serenebliss0/wavelet/src/mini/audio/drivers/Es8311Wire.cpp

#include "Es8311Wire.h"
#include <Wire.h>
#include <Arduino.h>

// -----------------------------------------------------------------------
// Register map (from Espressif's es8311_reg.h -- only what we use here)
// -----------------------------------------------------------------------
namespace
{
    constexpr uint8_t REG_RESET          = 0x00;
    constexpr uint8_t REG_CLK_MANAGER_01 = 0x01;
    constexpr uint8_t REG_CLK_MANAGER_02 = 0x02;
    constexpr uint8_t REG_CLK_MANAGER_03 = 0x03;
    constexpr uint8_t REG_CLK_MANAGER_04 = 0x04;
    constexpr uint8_t REG_CLK_MANAGER_05 = 0x05;
    constexpr uint8_t REG_CLK_MANAGER_06 = 0x06;
    constexpr uint8_t REG_CLK_MANAGER_07 = 0x07;
    constexpr uint8_t REG_CLK_MANAGER_08 = 0x08;
    constexpr uint8_t REG_SDPIN_09       = 0x09;
    constexpr uint8_t REG_SDPOUT_0A      = 0x0A;
    constexpr uint8_t REG_SYSTEM_0D      = 0x0D;
    constexpr uint8_t REG_SYSTEM_0E      = 0x0E;
    constexpr uint8_t REG_SYSTEM_12      = 0x12;
    constexpr uint8_t REG_SYSTEM_13      = 0x13;
    constexpr uint8_t REG_SYSTEM_14      = 0x14;
    constexpr uint8_t REG_ADC_16         = 0x16;
    constexpr uint8_t REG_ADC_17         = 0x17;
    constexpr uint8_t REG_ADC_1C         = 0x1C;
    constexpr uint8_t REG_DAC_31         = 0x31;
    constexpr uint8_t REG_DAC_32         = 0x32;
    constexpr uint8_t REG_DAC_37         = 0x37;

    // Clock coefficient table -- copied verbatim from Espressif's reference
    // driver. Same MCLK/rate combos, same divider values. This is just data,
    // the chip's datasheet dictates these, so it's ported as-is.
    struct CoeffDiv
    {
        uint32_t mclk;
        uint32_t rate;
        uint8_t  pre_div;
        uint8_t  pre_multi;
        uint8_t  adc_div;
        uint8_t  dac_div;
        uint8_t  fs_mode;
        uint8_t  lrck_h;
        uint8_t  lrck_l;
        uint8_t  bclk_div;
        uint8_t  adc_osr;
        uint8_t  dac_osr;
    };

    const CoeffDiv kCoeffDiv[] = {
        // 8k
        {12288000, 8000, 0x06, 0x00, 0x01, 0x01, 0x00, 0x00, 0xff, 0x04, 0x10, 0x10},
        {18432000, 8000, 0x03, 0x01, 0x03, 0x03, 0x00, 0x05, 0xff, 0x18, 0x10, 0x10},
        {16384000, 8000, 0x08, 0x00, 0x01, 0x01, 0x00, 0x00, 0xff, 0x04, 0x10, 0x10},
        {8192000,  8000, 0x04, 0x00, 0x01, 0x01, 0x00, 0x00, 0xff, 0x04, 0x10, 0x10},
        {6144000,  8000, 0x03, 0x00, 0x01, 0x01, 0x00, 0x00, 0xff, 0x04, 0x10, 0x10},
        {4096000,  8000, 0x02, 0x00, 0x01, 0x01, 0x00, 0x00, 0xff, 0x04, 0x10, 0x10},
        {3072000,  8000, 0x01, 0x00, 0x01, 0x01, 0x00, 0x00, 0xff, 0x04, 0x10, 0x10},
        {2048000,  8000, 0x01, 0x00, 0x01, 0x01, 0x00, 0x00, 0xff, 0x04, 0x10, 0x10},
        {1536000,  8000, 0x03, 0x02, 0x01, 0x01, 0x00, 0x00, 0xff, 0x04, 0x10, 0x10},
        {1024000,  8000, 0x01, 0x01, 0x01, 0x01, 0x00, 0x00, 0xff, 0x04, 0x10, 0x10},

        // 11.025k
        {11289600, 11025, 0x04, 0x00, 0x01, 0x01, 0x00, 0x00, 0xff, 0x04, 0x10, 0x10},
        {5644800,  11025, 0x02, 0x00, 0x01, 0x01, 0x00, 0x00, 0xff, 0x04, 0x10, 0x10},
        {2822400,  11025, 0x01, 0x00, 0x01, 0x01, 0x00, 0x00, 0xff, 0x04, 0x10, 0x10},
        {1411200,  11025, 0x01, 0x01, 0x01, 0x01, 0x00, 0x00, 0xff, 0x04, 0x10, 0x10},

        // 12k
        {12288000, 12000, 0x04, 0x00, 0x01, 0x01, 0x00, 0x00, 0xff, 0x04, 0x10, 0x10},
        {6144000,  12000, 0x02, 0x00, 0x01, 0x01, 0x00, 0x00, 0xff, 0x04, 0x10, 0x10},
        {3072000,  12000, 0x01, 0x00, 0x01, 0x01, 0x00, 0x00, 0xff, 0x04, 0x10, 0x10},
        {1536000,  12000, 0x01, 0x01, 0x01, 0x01, 0x00, 0x00, 0xff, 0x04, 0x10, 0x10},

        // 16k
        {12288000, 16000, 0x03, 0x00, 0x01, 0x01, 0x00, 0x00, 0xff, 0x04, 0x10, 0x10},
        {18432000, 16000, 0x03, 0x01, 0x03, 0x03, 0x00, 0x02, 0xff, 0x0c, 0x10, 0x10},
        {16384000, 16000, 0x04, 0x00, 0x01, 0x01, 0x00, 0x00, 0xff, 0x04, 0x10, 0x10},
        {8192000,  16000, 0x02, 0x00, 0x01, 0x01, 0x00, 0x00, 0xff, 0x04, 0x10, 0x10},
        {6144000,  16000, 0x03, 0x01, 0x01, 0x01, 0x00, 0x00, 0xff, 0x04, 0x10, 0x10},
        {4096000,  16000, 0x01, 0x00, 0x01, 0x01, 0x00, 0x00, 0xff, 0x04, 0x10, 0x10},
        {3072000,  16000, 0x03, 0x02, 0x01, 0x01, 0x00, 0x00, 0xff, 0x04, 0x10, 0x10},
        {2048000,  16000, 0x01, 0x01, 0x01, 0x01, 0x00, 0x00, 0xff, 0x04, 0x10, 0x10},
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
        {5644800,  88200, 0x01, 0x02, 0x01, 0x01, 0x00, 0x00, 0xff, 0x04, 0x10, 0x10},
        {2822400,  88200, 0x01, 0x03, 0x01, 0x01, 0x00, 0x00, 0xff, 0x04, 0x10, 0x10},
        {1411200,  88200, 0x01, 0x03, 0x01, 0x01, 0x01, 0x00, 0x7f, 0x02, 0x10, 0x10},

        // 96k
        {12288000, 96000, 0x01, 0x01, 0x01, 0x01, 0x00, 0x00, 0xff, 0x04, 0x10, 0x10},
        {18432000, 96000, 0x03, 0x02, 0x01, 0x01, 0x00, 0x00, 0xff, 0x04, 0x10, 0x10},
        {6144000,  96000, 0x01, 0x02, 0x01, 0x01, 0x00, 0x00, 0xff, 0x04, 0x10, 0x10},
        {3072000,  96000, 0x01, 0x03, 0x01, 0x01, 0x00, 0x00, 0xff, 0x04, 0x10, 0x10},
        {1536000,  96000, 0x01, 0x03, 0x01, 0x01, 0x01, 0x00, 0x7f, 0x02, 0x10, 0x10},
    };

    int getCoeff(uint32_t mclk, uint32_t rate)
    {
        for (size_t i = 0; i < sizeof(kCoeffDiv) / sizeof(kCoeffDiv[0]); i++)
        {
            if (kCoeffDiv[i].rate == rate && kCoeffDiv[i].mclk == mclk)
                return (int)i;
        }
        return -1;
    }

    uint8_t resolutionBits(Es8311Resolution res)
    {
        switch (res)
        {
            case Es8311Resolution::Res16: return 3 << 2;
            case Es8311Resolution::Res18: return 2 << 2;
            case Es8311Resolution::Res20: return 1 << 2;
            case Es8311Resolution::Res24: return 0 << 2;
            case Es8311Resolution::Res32: return 4 << 2;
        }
        return 3 << 2;
    }
}

bool Es8311Codec::writeReg(uint8_t reg, uint8_t val)
{
    Wire.beginTransmission(addr);
    Wire.write(reg);
    Wire.write(val);
    return Wire.endTransmission() == 0;
}

bool Es8311Codec::readReg(uint8_t reg, uint8_t* valOut)
{
    Wire.beginTransmission(addr);
    Wire.write(reg);
    if (Wire.endTransmission(false) != 0) // repeated start, keep bus held
        return false;

    if (Wire.requestFrom((int)addr, 1) != 1)
        return false;

    *valOut = Wire.read();
    return true;
}

bool Es8311Codec::sampleFrequencyConfig(int mclkFrequency, int sampleFrequency)
{
    int coeff = getCoeff((uint32_t)mclkFrequency, (uint32_t)sampleFrequency);
    if (coeff < 0)
        return false; // no matching row -- this MCLK/rate combo isn't supported by the chip

    const CoeffDiv& c = kCoeffDiv[coeff];
    uint8_t regv;

    if (!readReg(REG_CLK_MANAGER_02, &regv)) return false;
    regv &= 0x07;
    regv |= (c.pre_div - 1) << 5;
    regv |= c.pre_multi << 3;
    if (!writeReg(REG_CLK_MANAGER_02, regv)) return false;

    if (!writeReg(REG_CLK_MANAGER_03, (c.fs_mode << 6) | c.adc_osr)) return false;
    if (!writeReg(REG_CLK_MANAGER_04, c.dac_osr)) return false;
    if (!writeReg(REG_CLK_MANAGER_05, ((c.adc_div - 1) << 4) | (c.dac_div - 1))) return false;

    if (!readReg(REG_CLK_MANAGER_06, &regv)) return false;
    regv &= 0xE0;
    regv |= (c.bclk_div < 19) ? (c.bclk_div - 1) : c.bclk_div;
    if (!writeReg(REG_CLK_MANAGER_06, regv)) return false;

    if (!readReg(REG_CLK_MANAGER_07, &regv)) return false;
    regv &= 0xC0;
    regv |= c.lrck_h;
    if (!writeReg(REG_CLK_MANAGER_07, regv)) return false;

    if (!writeReg(REG_CLK_MANAGER_08, c.lrck_l)) return false;

    return true;
}

bool Es8311Codec::clockConfig(const Es8311ClockConfig& clkCfg, Es8311Resolution res)
{
    uint8_t reg06;
    uint8_t reg01 = 0x3F; // enable all internal clocks
    int mclkHz;

    if (clkCfg.mclk_from_mclk_pin)
    {
        mclkHz = clkCfg.mclk_frequency;
    }
    else
    {
        mclkHz = clkCfg.sample_frequency * (int)res * 2;
        reg01 |= (1 << 7); // take clock from BCLK/SCK pin instead
    }

    if (clkCfg.mclk_inverted)
        reg01 |= (1 << 6);

    if (!writeReg(REG_CLK_MANAGER_01, reg01)) return false;

    if (!readReg(REG_CLK_MANAGER_06, &reg06)) return false;
    if (clkCfg.sclk_inverted)
        reg06 |= (1 << 5);
    else
        reg06 &= ~(1 << 5);
    if (!writeReg(REG_CLK_MANAGER_06, reg06)) return false;

    return sampleFrequencyConfig(mclkHz, clkCfg.sample_frequency);
}

bool Es8311Codec::fmtConfig(Es8311Resolution resIn, Es8311Resolution resOut)
{
    uint8_t reg00;
    if (!readReg(REG_RESET, &reg00)) return false;
    reg00 &= 0xBF; // slave serial port mode (default)
    if (!writeReg(REG_RESET, reg00)) return false;

    uint8_t reg09 = resolutionBits(resIn);
    uint8_t reg0a = resolutionBits(resOut);

    if (!writeReg(REG_SDPIN_09, reg09)) return false;
    if (!writeReg(REG_SDPOUT_0A, reg0a)) return false;

    return true;
}

bool Es8311Codec::init(uint8_t i2cAddr, const Es8311ClockConfig& clkCfg,
                        Es8311Resolution resIn, Es8311Resolution resOut)
{
    addr = i2cAddr;

    if (clkCfg.sample_frequency < 8000 || clkCfg.sample_frequency > 96000)
        return false;

    if (!clkCfg.mclk_from_mclk_pin && resIn != resOut)
        return false; // driver requires matching in/out resolution when clocking off SCK

    // Reset to default, then power on.
    if (!writeReg(REG_RESET, 0x1F)) return false;
    delay(20);
    if (!writeReg(REG_RESET, 0x00)) return false;
    if (!writeReg(REG_RESET, 0x80)) return false;

    if (!clockConfig(clkCfg, resOut)) return false;
    if (!fmtConfig(resIn, resOut)) return false;

    if (!writeReg(REG_SYSTEM_0D, 0x01)) return false; // power up analog circuitry
    if (!writeReg(REG_SYSTEM_0E, 0x02)) return false; // enable analog PGA + ADC modulator
    if (!writeReg(REG_SYSTEM_12, 0x00)) return false; // power up DAC
    if (!writeReg(REG_SYSTEM_13, 0x10)) return false; // enable output to speaker/HP drive
    if (!writeReg(REG_ADC_1C, 0x6A)) return false;     // ADC equalizer bypass, cancel DC offset
    if (!writeReg(REG_DAC_37, 0x08)) return false;     // bypass DAC equalizer

    return true;
}

bool Es8311Codec::volumeSet(int volume, int* volumeSetOut)
{
    if (volume < 0) volume = 0;
    if (volume > 100) volume = 100;

    uint8_t reg32 = (volume == 0) ? 0 : (uint8_t)(((volume) * 256 / 100) - 1);

    if (volumeSetOut != nullptr)
        *volumeSetOut = volume;

    return writeReg(REG_DAC_32, reg32);
}

bool Es8311Codec::volumeGet(int* volumeOut)
{
    uint8_t reg32;
    if (!readReg(REG_DAC_32, &reg32)) return false;

    *volumeOut = (reg32 == 0) ? 0 : ((reg32 * 100) / 256) + 1;
    return true;
}

bool Es8311Codec::voiceMute(bool enable)
{
    uint8_t reg31;
    if (!readReg(REG_DAC_31, &reg31)) return false;

    if (enable)
        reg31 |= (1 << 6) | (1 << 5);
    else
        reg31 &= ~((1 << 6) | (1 << 5));

    return writeReg(REG_DAC_31, reg31);
}

bool Es8311Codec::microphoneConfig(bool digitalMic)
{
    uint8_t reg14 = 0x1A; // matches reference driver default
    if (digitalMic)
        reg14 |= (1 << 6);

    if (!writeReg(REG_ADC_17, 0xA8)) return false; // matches reference driver, harmless with mic unused
    return writeReg(REG_SYSTEM_14, reg14);
}
