serenebliss0/wavelet/src/mini/display/touch.cpp

#include "touch.h"

int touch_last_x = 0, touch_last_y = 0;
unsigned short int width=0, height=0, rotation,min_x=0,max_x=0,min_y=0,max_y=0;

FT6336 ts = FT6336(TOUCH_FT6336_SDA, TOUCH_FT6336_SCL, TOUCH_FT6336_INT, TOUCH_FT6336_RST, max(TOUCH_MAP_X1, TOUCH_MAP_X2), max(TOUCH_MAP_Y1, TOUCH_MAP_Y2));

void touch_init(unsigned short int w, unsigned short int h,unsigned char r)
{
  width = w; 
  height = h;
  switch (r){
    case ROTATION_NORMAL:
    case ROTATION_INVERTED:
      min_x = TOUCH_MAP_X1;
      max_x = TOUCH_MAP_X2;
      min_y = TOUCH_MAP_Y1;
      max_y = TOUCH_MAP_Y2;
      break;
    case ROTATION_LEFT:
    case ROTATION_RIGHT:
      min_x = TOUCH_MAP_Y1;
      max_x = TOUCH_MAP_Y2;
      min_y = TOUCH_MAP_X1;
      max_y = TOUCH_MAP_X2;
      break;
    default:
      break;
  }
  ts.begin();
  ts.setRotation(r);
}

bool touch_touched(void)
{
   ts.read();
  if (ts.isTouched)
  {
//#if defined(TOUCH_SWAP_XY)
//    touch_last_x = map(ts.points[0].y, TOUCH_MAP_X1, TOUCH_MAP_X2, 0, width - 1);
//    touch_last_y = map(ts.points[0].x, TOUCH_MAP_Y1, TOUCH_MAP_Y2, 0, height - 1);
//#else
    touch_last_x = map(ts.points[0].x, min_x, max_x, 0, width - 1);
    touch_last_y = map(ts.points[0].y, min_y, max_y, 0, height - 1);
//#endif
//    Serial.print("x = ");
//    Serial.print(touch_last_x);
//    Serial.print(", y = ");
//    Serial.print(touch_last_y);
//    Serial.print("\r\n");
    return true;
  }
  else
  {
    return false;
  }
}

bool touch_has_signal(void)
{
  return true;
}

bool touch_released(void)
{
  return true;
}
