serenebliss0/wavelet/src/mini/storage/Paths.h

namespace Paths
{
    constexpr auto SYSTEM  = "/system";
    constexpr auto CONFIG  = "/config";
    constexpr auto CACHE   = "/cache";
    constexpr auto MEDIA   = "/media";
    constexpr auto LOGS    = "/logs";
    constexpr auto UPDATES = "/updates";

    constexpr auto SETTINGS = "/config/settings.json";
    constexpr auto DEVICE   = "/system/device.json";
    constexpr auto README   = "/README.txt";
}
