serenebliss0/wavelet/src/mini/wavelet-mini-screens/src/ui/ui.c

#include "ui.h"
#include "screens.h"
#include "images.h"
#include "actions.h"
#include "vars.h"

// ASSETS DEFINITION
const uint8_t assets[4652] = {
    0x7E, 0x45, 0x45, 0x5A, 0x03, 0x00, 0x06, 0x00, 0x00, 0x00, 0x00, 0x00, 0x24, 0x00, 0x00, 0x00,
    0x24, 0x00, 0x00, 0x00, 0x00, 0x00, 0x00, 0x00, 0x00, 0x00, 0x00, 0x00, 0x00, 0x00, 0x00, 0x00,
    0x00, 0x00, 0x00, 0x00, 0x20, 0x00, 0x00, 0x00, 0x00, 0x00, 0x00, 0x00, 0x00, 0x00, 0x00, 0x00,
    0x40, 0x01, 0xF0, 0x00, 0x02, 0x00, 0x00, 0x00, 0x24, 0x00, 0x00, 0x00, 0x02, 0x00, 0x00, 0x00,
    0x24, 0x00, 0x00, 0x00, 0x0A, 0x00, 0x00, 0x00, 0x20, 0x00, 0x00, 0x00, 0x0D, 0x00, 0x00, 0x00,
    0xA0, 0x10, 0x00, 0x00, 0x06, 0x00, 0x00, 0x00, 0x38, 0x00, 0x00, 0x00, 0x4C, 0x00, 0x00, 0x00,
    0x54, 0x00, 0x00, 0x00, 0x00, 0x00, 0xFF, 0xFF, 0x58, 0x00, 0x00, 0x00, 0x84, 0x00, 0x00, 0x00,
    0xB0, 0x00, 0x00, 0x00, 0xDC, 0x00, 0x00, 0x00, 0x08, 0x01, 0x00, 0x00, 0x34, 0x01, 0x00, 0x00,
    0x60, 0x01, 0x00, 0x00, 0x8C, 0x01, 0x00, 0x00, 0xB8, 0x01, 0x00, 0x00, 0xE4, 0x01, 0x00, 0x00,
    0x14, 0x02, 0x00, 0x00, 0x20, 0x02, 0x00, 0x00, 0x2C, 0x02, 0x00, 0x00, 0x38, 0x02, 0x00, 0x00,
    0x44, 0x02, 0x00, 0x00, 0x50, 0x02, 0x00, 0x00, 0x5C, 0x02, 0x00, 0x00, 0x0D, 0x00, 0x00, 0x00,
    0x60, 0x02, 0x00, 0x00, 0x78, 0x02, 0x00, 0x00, 0x0D, 0x00, 0x00, 0x00, 0x7C, 0x02, 0x00, 0x00,
    0x02, 0x00, 0x00, 0x00, 0x90, 0x02, 0x00, 0x00, 0x00, 0x00, 0x00, 0x00, 0x00, 0x00, 0x00, 0x00,
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
    { NATIVE_VAR_TYPE_NONE, 0, 0 },
};

ActionExecFunc actions[] = {
    0
};

void ui_init() {
    eez_flow_init(assets, sizeof(assets), (lv_obj_t **)&objects, sizeof(objects), images, sizeof(images), actions);
}

void ui_tick() {
    eez_flow_tick();
    tick_screen(g_currentScreen);
}
