serenebliss0/wavelet/src/mini/wavelet-mini-screens/src/ui/screens.c

#include <string.h>

#include "screens.h"
#include "images.h"
#include "fonts.h"
#include "actions.h"
#include "vars.h"
#include "styles.h"
#include "ui.h"

#include <string.h>

objects_t objects;

static const char *screen_names[] = { "BootSplash", "InitialQRPage", "Onboarding1", "Onboarding2", "Onboarding3", "DefaultClock", "VolumePane" };
static const char *object_names[] = { "boot_splash", "initial_qr_page", "onboarding1", "onboarding2", "onboarding3", "default_clock", "volume_pane", "wavelet_log", "obj0", "obj1", "obj2", "obj3", "obj4", "obj5", "obj6", "obj7", "obj8", "obj9", "obj10", "obj11", "obj12", "obj13", "obj14", "obj15", "obj16", "obj17", "obj18", "obj19", "wallpaper_image", "obj20", "obj21" };

//
// Event handlers
//

lv_obj_t *tick_value_change_obj;

static void event_handler_cb_onboarding1_obj8(lv_event_t *e) {
    lv_event_code_t event = lv_event_get_code(e);
    void *flowState = lv_event_get_user_data(e);
    (void)flowState;
    
    if (event == LV_EVENT_PRESSED) {
        e->user_data = (void *)0;
        flowPropagateValueLVGLEvent(flowState, 4, 0, e);
    }
}

static void event_handler_cb_onboarding2_obj12(lv_event_t *e) {
    lv_event_code_t event = lv_event_get_code(e);
    void *flowState = lv_event_get_user_data(e);
    (void)flowState;
    
    if (event == LV_EVENT_PRESSED) {
        e->user_data = (void *)0;
        flowPropagateValueLVGLEvent(flowState, 4, 0, e);
    }
}

static void event_handler_cb_onboarding3_obj16(lv_event_t *e) {
    lv_event_code_t event = lv_event_get_code(e);
    void *flowState = lv_event_get_user_data(e);
    (void)flowState;
    
    if (event == LV_EVENT_PRESSED) {
        e->user_data = (void *)0;
        flowPropagateValueLVGLEvent(flowState, 4, 0, e);
    }
}

//
// Screens
//

void create_screen_boot_splash() {
    void *flowState = getFlowState(0, 0);
    (void)flowState;
    lv_obj_t *obj = lv_obj_create(0);
    objects.boot_splash = obj;
    lv_obj_set_pos(obj, 0, 0);
    lv_obj_set_size(obj, 320, 240);
    lv_obj_clear_flag(obj, LV_OBJ_FLAG_CLICK_FOCUSABLE|LV_OBJ_FLAG_SNAPPABLE|LV_OBJ_FLAG_SCROLLABLE|LV_OBJ_FLAG_SCROLL_ELASTIC|LV_OBJ_FLAG_SCROLL_CHAIN_HOR);
    lv_obj_set_style_bg_color(obj, lv_color_hex(theme_colors[eez_flow_get_selected_theme_index()][0]), LV_PART_MAIN | LV_STATE_DEFAULT);
    {
        lv_obj_t *parent_obj = obj;
        {
            // wavelet_log
            lv_obj_t *obj = lv_img_create(parent_obj);
            objects.wavelet_log = obj;
            lv_obj_set_pos(obj, 91, 96);
            lv_obj_set_size(obj, LV_SIZE_CONTENT, LV_SIZE_CONTENT);
            lv_img_set_src(obj, &img_wavelet_logo);
            lv_obj_set_style_align(obj, LV_ALIGN_DEFAULT, LV_PART_MAIN | LV_STATE_DEFAULT);
        }
    }
    
    tick_screen_boot_splash();
}

void tick_screen_boot_splash() {
    void *flowState = getFlowState(0, 0);
    (void)flowState;
}

void create_screen_initial_qr_page() {
    void *flowState = getFlowState(0, 1);
    (void)flowState;
    lv_obj_t *obj = lv_obj_create(0);
    objects.initial_qr_page = obj;
    lv_obj_set_pos(obj, 0, 0);
    lv_obj_set_size(obj, 320, 240);
    lv_obj_clear_flag(obj, LV_OBJ_FLAG_CLICK_FOCUSABLE);
    lv_obj_set_style_bg_color(obj, lv_color_hex(theme_colors[eez_flow_get_selected_theme_index()][0]), LV_PART_MAIN | LV_STATE_DEFAULT);
    {
        lv_obj_t *parent_obj = obj;
        {
            lv_obj_t *obj = lv_qrcode_create(parent_obj, 96, lv_color_hex(0x000000), lv_color_hex(0xffffff));
            objects.obj0 = obj;
            lv_obj_set_pos(obj, 10, 72);
            lv_obj_set_size(obj, 96, 96);
            lv_qrcode_update(obj, "{generatedPayloadToken}", 23);
            lv_obj_add_flag(obj, LV_OBJ_FLAG_CLICKABLE);
            lv_obj_set_style_border_color(obj, lv_color_hex(0x000000), LV_PART_MAIN | LV_STATE_DEFAULT);
            lv_obj_set_style_outline_width(obj, 2, LV_PART_MAIN | LV_STATE_DEFAULT);
            lv_obj_set_style_radius(obj, 10, LV_PART_MAIN | LV_STATE_DEFAULT);
            lv_obj_set_style_outline_color(obj, lv_color_hex(theme_colors[eez_flow_get_selected_theme_index()][3]), LV_PART_MAIN | LV_STATE_DEFAULT);
            lv_obj_set_style_outline_opa(obj, 150, LV_PART_MAIN | LV_STATE_DEFAULT);
            lv_obj_set_style_shadow_width(obj, 4, LV_PART_MAIN | LV_STATE_DEFAULT);
            lv_obj_set_style_shadow_color(obj, lv_color_hex(0xff9d9d), LV_PART_MAIN | LV_STATE_DEFAULT);
        }
        {
            lv_obj_t *obj = lv_label_create(parent_obj);
            objects.obj1 = obj;
            lv_obj_set_pos(obj, 127, 72);
            lv_obj_set_size(obj, LV_SIZE_CONTENT, LV_SIZE_CONTENT);
            lv_obj_set_style_text_color(obj, lv_color_hex(theme_colors[eez_flow_get_selected_theme_index()][5]), LV_PART_MAIN | LV_STATE_DEFAULT);
            lv_obj_set_style_text_font(obj, &ui_font_nunito_18_bold, LV_PART_MAIN | LV_STATE_DEFAULT);
            lv_obj_set_style_text_letter_space(obj, 0, LV_PART_MAIN | LV_STATE_DEFAULT);
            lv_label_set_text_static(obj, "Connect to Wavelet");
        }
        {
            lv_obj_t *obj = lv_label_create(parent_obj);
            objects.obj2 = obj;
            lv_obj_set_pos(obj, 127, 98);
            lv_obj_set_size(obj, LV_SIZE_CONTENT, 45);
            lv_obj_set_style_width(obj, 163, LV_PART_MAIN | LV_STATE_DEFAULT);
            lv_obj_set_style_text_color(obj, lv_color_hex(theme_colors[eez_flow_get_selected_theme_index()][5]), LV_PART_MAIN | LV_STATE_DEFAULT);
            lv_obj_set_style_text_font(obj, &ui_font_inter_10, LV_PART_MAIN | LV_STATE_DEFAULT);
            lv_label_set_text_static(obj, "Open the Wavelet app on your phone and scan the QR code, or enter the code below.");
        }
        {
            lv_obj_t *obj = lv_obj_create(parent_obj);
            objects.obj3 = obj;
            lv_obj_set_pos(obj, 127, 143);
            lv_obj_set_size(obj, 163, 57);
            lv_obj_set_style_pad_left(obj, 0, LV_PART_MAIN | LV_STATE_DEFAULT);
            lv_obj_set_style_pad_top(obj, 0, LV_PART_MAIN | LV_STATE_DEFAULT);
            lv_obj_set_style_pad_right(obj, 0, LV_PART_MAIN | LV_STATE_DEFAULT);
            lv_obj_set_style_pad_bottom(obj, 0, LV_PART_MAIN | LV_STATE_DEFAULT);
            lv_obj_set_style_bg_opa(obj, 0, LV_PART_MAIN | LV_STATE_DEFAULT);
            lv_obj_set_style_border_width(obj, 0, LV_PART_MAIN | LV_STATE_DEFAULT);
            lv_obj_set_style_radius(obj, 8, LV_PART_MAIN | LV_STATE_DEFAULT);
            lv_obj_set_style_border_color(obj, lv_color_lighten(lv_color_hex(0x4f762e), 0), LV_PART_MAIN | LV_STATE_DEFAULT);
            lv_obj_set_style_bg_color(obj, lv_color_hex(0xccccff), LV_PART_MAIN | LV_STATE_DEFAULT);
        }
        {
            lv_obj_t *obj = lv_obj_create(parent_obj);
            objects.obj4 = obj;
            lv_obj_set_pos(obj, 127, 143);
            lv_obj_set_size(obj, 163, 57);
            lv_obj_set_style_bg_color(obj, lv_color_hex(0xf04f76), LV_PART_MAIN | LV_STATE_DEFAULT);
            lv_obj_set_style_bg_opa(obj, 20, LV_PART_MAIN | LV_STATE_DEFAULT);
            lv_obj_set_style_border_color(obj, lv_color_hex(0xf04f76), LV_PART_MAIN | LV_STATE_DEFAULT);
            lv_obj_set_style_radius(obj, 8, LV_PART_MAIN | LV_STATE_DEFAULT);
        }
        {
            lv_obj_t *obj = lv_label_create(parent_obj);
            objects.obj5 = obj;
            lv_obj_set_pos(obj, 135, 150);
            lv_obj_set_size(obj, LV_SIZE_CONTENT, LV_SIZE_CONTENT);
            lv_obj_set_style_bg_color(obj, lv_color_hex(theme_colors[eez_flow_get_selected_theme_index()][5]), LV_PART_MAIN | LV_STATE_DEFAULT);
            lv_obj_set_style_text_font(obj, &ui_font_inter_7, LV_PART_MAIN | LV_STATE_DEFAULT);
            lv_obj_set_style_text_color(obj, lv_color_hex(theme_colors[eez_flow_get_selected_theme_index()][5]), LV_PART_MAIN | LV_STATE_DEFAULT);
            lv_obj_set_style_text_letter_space(obj, 2, LV_PART_MAIN | LV_STATE_DEFAULT);
            lv_label_set_text_static(obj, "MANUAL CODE");
        }
        {
            lv_obj_t *obj = lv_label_create(parent_obj);
            objects.obj6 = obj;
            lv_obj_set_pos(obj, 135, 165);
            lv_obj_set_size(obj, LV_SIZE_CONTENT, LV_SIZE_CONTENT);
            lv_obj_set_style_text_color(obj, lv_color_hex(theme_colors[eez_flow_get_selected_theme_index()][5]), LV_PART_MAIN | LV_STATE_DEFAULT);
            lv_obj_set_style_text_font(obj, &lv_font_montserrat_18, LV_PART_MAIN | LV_STATE_DEFAULT);
            lv_label_set_text(obj, "");
        }
    }
    
    tick_screen_initial_qr_page();
}

void tick_screen_initial_qr_page() {
    void *flowState = getFlowState(0, 1);
    (void)flowState;
    {
        const char *new_val = evalTextProperty(flowState, 7, 3, "Failed to evaluate Text in Label widget");
        const char *cur_val = lv_label_get_text(objects.obj6);
        if (strcmp(new_val, cur_val) != 0) {
            tick_value_change_obj = objects.obj6;
            lv_label_set_text(objects.obj6, new_val);
            tick_value_change_obj = NULL;
        }
    }
}

void create_screen_onboarding1() {
    void *flowState = getFlowState(0, 2);
    (void)flowState;
    lv_obj_t *obj = lv_obj_create(0);
    objects.onboarding1 = obj;
    lv_obj_set_pos(obj, 0, 0);
    lv_obj_set_size(obj, 320, 240);
    lv_obj_set_style_bg_color(obj, lv_color_hex(theme_colors[eez_flow_get_selected_theme_index()][0]), LV_PART_MAIN | LV_STATE_DEFAULT);
    {
        lv_obj_t *parent_obj = obj;
        {
            lv_obj_t *obj = lv_label_create(parent_obj);
            objects.obj7 = obj;
            lv_obj_set_pos(obj, 11, 21);
            lv_obj_set_size(obj, LV_SIZE_CONTENT, LV_SIZE_CONTENT);
            lv_obj_set_style_text_font(obj, &ui_font_nunito_18_bold, LV_PART_MAIN | LV_STATE_DEFAULT);
            lv_obj_set_style_text_color(obj, lv_color_hex(theme_colors[eez_flow_get_selected_theme_index()][5]), LV_PART_MAIN | LV_STATE_DEFAULT);
            lv_label_set_text_static(obj, "Quick Settings");
        }
        {
            lv_obj_t *obj = lv_img_create(parent_obj);
            lv_obj_set_pos(obj, 11, 71);
            lv_obj_set_size(obj, LV_SIZE_CONTENT, LV_SIZE_CONTENT);
            lv_img_set_src(obj, &img_onboarding_tutorial_1_swipedown);
        }
        {
            lv_obj_t *obj = lv_img_create(parent_obj);
            lv_obj_set_pos(obj, 114, 217);
            lv_obj_set_size(obj, LV_SIZE_CONTENT, LV_SIZE_CONTENT);
            lv_img_set_src(obj, &img_3_step_guide_phase_1);
        }
        {
            lv_obj_t *obj = lv_btn_create(parent_obj);
            objects.obj8 = obj;
            lv_obj_set_pos(obj, 245, 203);
            lv_obj_set_size(obj, 64, 29);
            lv_obj_add_event_cb(obj, event_handler_cb_onboarding1_obj8, LV_EVENT_ALL, flowState);
            lv_obj_set_style_radius(obj, 7, LV_PART_MAIN | LV_STATE_DEFAULT);
            lv_obj_set_style_bg_color(obj, lv_color_hex(theme_colors[eez_flow_get_selected_theme_index()][2]), LV_PART_MAIN | LV_STATE_DEFAULT);
            {
                lv_obj_t *parent_obj = obj;
                {
                    lv_obj_t *obj = lv_label_create(parent_obj);
                    objects.obj9 = obj;
                    lv_obj_set_pos(obj, 0, 0);
                    lv_obj_set_size(obj, LV_SIZE_CONTENT, LV_SIZE_CONTENT);
                    lv_obj_set_style_align(obj, LV_ALIGN_CENTER, LV_PART_MAIN | LV_STATE_DEFAULT);
                    lv_obj_set_style_text_color(obj, lv_color_hex(theme_colors[eez_flow_get_selected_theme_index()][5]), LV_PART_MAIN | LV_STATE_DEFAULT);
                    lv_obj_set_style_text_font(obj, &lv_font_montserrat_10, LV_PART_MAIN | LV_STATE_DEFAULT);
                    lv_label_set_text_static(obj, "Next");
                }
            }
        }
        {
            lv_obj_t *obj = lv_label_create(parent_obj);
            objects.obj10 = obj;
            lv_obj_set_pos(obj, 134, 80);
            lv_obj_set_size(obj, LV_SIZE_CONTENT, LV_SIZE_CONTENT);
            lv_obj_set_style_text_color(obj, lv_color_hex(theme_colors[eez_flow_get_selected_theme_index()][5]), LV_PART_MAIN | LV_STATE_DEFAULT);
            lv_obj_set_style_text_font(obj, &lv_font_montserrat_12, LV_PART_MAIN | LV_STATE_DEFAULT);
            lv_obj_set_style_width(obj, 172, LV_PART_MAIN | LV_STATE_DEFAULT);
            lv_obj_set_style_text_line_space(obj, 2, LV_PART_MAIN | LV_STATE_DEFAULT);
            lv_label_set_text_static(obj, "Access WiFi, brightness, and Spotify connect with a downward swipe from anywhere on the screen.");
        }
    }
    
    tick_screen_onboarding1();
}

void tick_screen_onboarding1() {
    void *flowState = getFlowState(0, 2);
    (void)flowState;
}

void create_screen_onboarding2() {
    void *flowState = getFlowState(0, 3);
    (void)flowState;
    lv_obj_t *obj = lv_obj_create(0);
    objects.onboarding2 = obj;
    lv_obj_set_pos(obj, 0, 0);
    lv_obj_set_size(obj, 320, 240);
    lv_obj_set_style_bg_color(obj, lv_color_hex(theme_colors[eez_flow_get_selected_theme_index()][0]), LV_PART_MAIN | LV_STATE_DEFAULT);
    {
        lv_obj_t *parent_obj = obj;
        {
            lv_obj_t *obj = lv_label_create(parent_obj);
            objects.obj11 = obj;
            lv_obj_set_pos(obj, 11, 21);
            lv_obj_set_size(obj, LV_SIZE_CONTENT, LV_SIZE_CONTENT);
            lv_obj_set_style_text_font(obj, &ui_font_nunito_18_bold, LV_PART_MAIN | LV_STATE_DEFAULT);
            lv_obj_set_style_text_color(obj, lv_color_hex(theme_colors[eez_flow_get_selected_theme_index()][5]), LV_PART_MAIN | LV_STATE_DEFAULT);
            lv_label_set_text_static(obj, "Widgets");
        }
        {
            lv_obj_t *obj = lv_img_create(parent_obj);
            lv_obj_set_pos(obj, 11, 71);
            lv_obj_set_size(obj, LV_SIZE_CONTENT, LV_SIZE_CONTENT);
            lv_img_set_src(obj, &img_onboarding_tutorial_2_leftright);
        }
        {
            lv_obj_t *obj = lv_img_create(parent_obj);
            lv_obj_set_pos(obj, 114, 217);
            lv_obj_set_size(obj, LV_SIZE_CONTENT, LV_SIZE_CONTENT);
            lv_img_set_src(obj, &img_3_step_guide_phase_2);
        }
        {
            lv_obj_t *obj = lv_btn_create(parent_obj);
            objects.obj12 = obj;
            lv_obj_set_pos(obj, 245, 203);
            lv_obj_set_size(obj, 64, 29);
            lv_obj_add_event_cb(obj, event_handler_cb_onboarding2_obj12, LV_EVENT_ALL, flowState);
            lv_obj_set_style_radius(obj, 7, LV_PART_MAIN | LV_STATE_DEFAULT);
            lv_obj_set_style_bg_color(obj, lv_color_hex(theme_colors[eez_flow_get_selected_theme_index()][2]), LV_PART_MAIN | LV_STATE_DEFAULT);
            {
                lv_obj_t *parent_obj = obj;
                {
                    lv_obj_t *obj = lv_label_create(parent_obj);
                    objects.obj13 = obj;
                    lv_obj_set_pos(obj, 0, 0);
                    lv_obj_set_size(obj, LV_SIZE_CONTENT, LV_SIZE_CONTENT);
                    lv_obj_set_style_align(obj, LV_ALIGN_CENTER, LV_PART_MAIN | LV_STATE_DEFAULT);
                    lv_obj_set_style_text_color(obj, lv_color_hex(theme_colors[eez_flow_get_selected_theme_index()][5]), LV_PART_MAIN | LV_STATE_DEFAULT);
                    lv_obj_set_style_text_font(obj, &lv_font_montserrat_10, LV_PART_MAIN | LV_STATE_DEFAULT);
                    lv_label_set_text_static(obj, "Next");
                }
            }
        }
        {
            lv_obj_t *obj = lv_label_create(parent_obj);
            objects.obj14 = obj;
            lv_obj_set_pos(obj, 134, 80);
            lv_obj_set_size(obj, LV_SIZE_CONTENT, LV_SIZE_CONTENT);
            lv_obj_set_style_text_color(obj, lv_color_hex(theme_colors[eez_flow_get_selected_theme_index()][5]), LV_PART_MAIN | LV_STATE_DEFAULT);
            lv_obj_set_style_text_font(obj, &lv_font_montserrat_12, LV_PART_MAIN | LV_STATE_DEFAULT);
            lv_obj_set_style_width(obj, 172, LV_PART_MAIN | LV_STATE_DEFAULT);
            lv_obj_set_style_text_line_space(obj, 2, LV_PART_MAIN | LV_STATE_DEFAULT);
            lv_label_set_text_static(obj, "Browse your widgets: weather, timers, and more by swiping left or right on the main screen.");
        }
    }
    
    tick_screen_onboarding2();
}

void tick_screen_onboarding2() {
    void *flowState = getFlowState(0, 3);
    (void)flowState;
}

void create_screen_onboarding3() {
    void *flowState = getFlowState(0, 4);
    (void)flowState;
    lv_obj_t *obj = lv_obj_create(0);
    objects.onboarding3 = obj;
    lv_obj_set_pos(obj, 0, 0);
    lv_obj_set_size(obj, 320, 240);
    lv_obj_set_style_bg_color(obj, lv_color_hex(theme_colors[eez_flow_get_selected_theme_index()][0]), LV_PART_MAIN | LV_STATE_DEFAULT);
    {
        lv_obj_t *parent_obj = obj;
        {
            lv_obj_t *obj = lv_label_create(parent_obj);
            objects.obj15 = obj;
            lv_obj_set_pos(obj, 11, 21);
            lv_obj_set_size(obj, LV_SIZE_CONTENT, LV_SIZE_CONTENT);
            lv_obj_set_style_text_font(obj, &ui_font_nunito_18_bold, LV_PART_MAIN | LV_STATE_DEFAULT);
            lv_obj_set_style_text_color(obj, lv_color_hex(theme_colors[eez_flow_get_selected_theme_index()][5]), LV_PART_MAIN | LV_STATE_DEFAULT);
            lv_label_set_text_static(obj, "Always On Clock");
        }
        {
            lv_obj_t *obj = lv_img_create(parent_obj);
            lv_obj_set_pos(obj, 11, 71);
            lv_obj_set_size(obj, LV_SIZE_CONTENT, LV_SIZE_CONTENT);
            lv_img_set_src(obj, &img_onboarding_tutorial_3_swipeup);
        }
        {
            lv_obj_t *obj = lv_img_create(parent_obj);
            lv_obj_set_pos(obj, 114, 217);
            lv_obj_set_size(obj, LV_SIZE_CONTENT, LV_SIZE_CONTENT);
            lv_img_set_src(obj, &img_3_step_guide_phase_3);
        }
        {
            lv_obj_t *obj = lv_btn_create(parent_obj);
            objects.obj16 = obj;
            lv_obj_set_pos(obj, 245, 203);
            lv_obj_set_size(obj, 64, 29);
            lv_obj_add_event_cb(obj, event_handler_cb_onboarding3_obj16, LV_EVENT_ALL, flowState);
            lv_obj_set_style_radius(obj, 7, LV_PART_MAIN | LV_STATE_DEFAULT);
            lv_obj_set_style_bg_color(obj, lv_color_hex(theme_colors[eez_flow_get_selected_theme_index()][1]), LV_PART_MAIN | LV_STATE_DEFAULT);
            {
                lv_obj_t *parent_obj = obj;
                {
                    lv_obj_t *obj = lv_label_create(parent_obj);
                    objects.obj17 = obj;
                    lv_obj_set_pos(obj, 0, 0);
                    lv_obj_set_size(obj, LV_SIZE_CONTENT, LV_SIZE_CONTENT);
                    lv_obj_set_style_align(obj, LV_ALIGN_CENTER, LV_PART_MAIN | LV_STATE_DEFAULT);
                    lv_obj_set_style_text_color(obj, lv_color_hex(theme_colors[eez_flow_get_selected_theme_index()][5]), LV_PART_MAIN | LV_STATE_DEFAULT);
                    lv_obj_set_style_text_font(obj, &lv_font_montserrat_10, LV_PART_MAIN | LV_STATE_DEFAULT);
                    lv_label_set_text_static(obj, "Finish");
                }
            }
        }
        {
            lv_obj_t *obj = lv_label_create(parent_obj);
            objects.obj18 = obj;
            lv_obj_set_pos(obj, 134, 80);
            lv_obj_set_size(obj, LV_SIZE_CONTENT, LV_SIZE_CONTENT);
            lv_obj_set_style_text_color(obj, lv_color_hex(theme_colors[eez_flow_get_selected_theme_index()][5]), LV_PART_MAIN | LV_STATE_DEFAULT);
            lv_obj_set_style_text_font(obj, &lv_font_montserrat_12, LV_PART_MAIN | LV_STATE_DEFAULT);
            lv_obj_set_style_width(obj, 172, LV_PART_MAIN | LV_STATE_DEFAULT);
            lv_obj_set_style_text_line_space(obj, 2, LV_PART_MAIN | LV_STATE_DEFAULT);
            lv_label_set_text_static(obj, "Swipe up for a minimal always-on display that stays visible even when the screen is dimmed.");
        }
    }
    
    tick_screen_onboarding3();
}

void tick_screen_onboarding3() {
    void *flowState = getFlowState(0, 4);
    (void)flowState;
}

void create_screen_default_clock() {
    void *flowState = getFlowState(0, 5);
    (void)flowState;
    lv_obj_t *obj = lv_obj_create(0);
    objects.default_clock = obj;
    lv_obj_set_pos(obj, 0, 0);
    lv_obj_set_size(obj, 320, 240);
    lv_obj_set_style_bg_color(obj, lv_color_hex(theme_colors[eez_flow_get_selected_theme_index()][0]), LV_PART_MAIN | LV_STATE_DEFAULT);
    {
        lv_obj_t *parent_obj = obj;
        {
            lv_obj_t *obj = lv_label_create(parent_obj);
            objects.obj20 = obj;
            lv_obj_set_pos(obj, 21, 13);
            lv_obj_set_size(obj, LV_SIZE_CONTENT, LV_SIZE_CONTENT);
            lv_obj_set_style_width(obj, 1073741823, LV_PART_MAIN | LV_STATE_DEFAULT);
            lv_obj_set_style_height(obj, 1073741823, LV_PART_MAIN | LV_STATE_DEFAULT);
            lv_label_set_text(obj, "");
        }
        {
            lv_obj_t *obj = lv_label_create(parent_obj);
            lv_obj_set_pos(obj, 21, 20);
            lv_obj_set_size(obj, LV_SIZE_CONTENT, LV_SIZE_CONTENT);
            lv_obj_set_style_text_font(obj, &lv_font_montserrat_12, LV_PART_MAIN | LV_STATE_DEFAULT);
            lv_obj_set_style_width(obj, 10193, LV_PART_MAIN | LV_STATE_DEFAULT);
            lv_obj_set_style_height(obj, 10193, LV_PART_MAIN | LV_STATE_DEFAULT);
            lv_label_set_text_static(obj, "");
        }
        {
            lv_obj_t *obj = lv_label_create(parent_obj);
            objects.obj21 = obj;
            lv_obj_set_pos(obj, 38, 20);
            lv_obj_set_size(obj, LV_SIZE_CONTENT, LV_SIZE_CONTENT);
            lv_obj_set_style_text_font(obj, &lv_font_montserrat_12, LV_PART_MAIN | LV_STATE_DEFAULT);
            lv_label_set_text(obj, "");
        }
        {
            lv_obj_t *obj = lv_label_create(parent_obj);
            lv_obj_set_pos(obj, 251, 19);
            lv_obj_set_size(obj, LV_SIZE_CONTENT, LV_SIZE_CONTENT);
            lv_obj_set_style_text_font(obj, &lv_font_montserrat_12, LV_PART_MAIN | LV_STATE_DEFAULT);
            lv_label_set_text_static(obj, "");
        }
        {
            lv_obj_t *obj = lv_label_create(parent_obj);
            lv_obj_set_pos(obj, 282, 20);
            lv_obj_set_size(obj, LV_SIZE_CONTENT, LV_SIZE_CONTENT);
            lv_obj_set_style_text_font(obj, &lv_font_montserrat_12, LV_PART_MAIN | LV_STATE_DEFAULT);
            lv_label_set_text_static(obj, "");
        }
        {
            lv_obj_t *obj = lv_label_create(parent_obj);
            lv_obj_set_pos(obj, 57, 94);
            lv_obj_set_size(obj, LV_SIZE_CONTENT, LV_SIZE_CONTENT);
            lv_obj_set_style_text_font(obj, &lv_font_montserrat_48, LV_PART_MAIN | LV_STATE_DEFAULT);
            lv_label_set_text_static(obj, "hh");
        }
        {
            lv_obj_t *obj = lv_label_create(parent_obj);
            lv_obj_set_pos(obj, 185, 95);
            lv_obj_set_size(obj, LV_SIZE_CONTENT, LV_SIZE_CONTENT);
            lv_obj_set_style_text_font(obj, &lv_font_montserrat_48, LV_PART_MAIN | LV_STATE_DEFAULT);
            lv_label_set_text_static(obj, "hh");
        }
        {
            lv_obj_t *obj = lv_label_create(parent_obj);
            lv_obj_set_pos(obj, 149, 95);
            lv_obj_set_size(obj, LV_SIZE_CONTENT, LV_SIZE_CONTENT);
            lv_obj_set_style_text_font(obj, &lv_font_montserrat_48, LV_PART_MAIN | LV_STATE_DEFAULT);
            lv_label_set_text_static(obj, ":");
        }
        {
            lv_obj_t *obj = lv_label_create(parent_obj);
            lv_obj_set_pos(obj, 147, 161);
            lv_obj_set_size(obj, LV_SIZE_CONTENT, LV_SIZE_CONTENT);
            lv_obj_set_style_text_font(obj, &lv_font_montserrat_14, LV_PART_MAIN | LV_STATE_DEFAULT);
            lv_label_set_text_static(obj, "day");
        }
        {
            lv_obj_t *obj = lv_label_create(parent_obj);
            lv_obj_set_pos(obj, 144, 177);
            lv_obj_set_size(obj, LV_SIZE_CONTENT, LV_SIZE_CONTENT);
            lv_obj_set_style_text_font(obj, &lv_font_montserrat_14, LV_PART_MAIN | LV_STATE_DEFAULT);
            lv_obj_set_style_align(obj, LV_ALIGN_DEFAULT, LV_PART_MAIN | LV_STATE_DEFAULT);
            lv_label_set_text_static(obj, "date");
        }
        {
            lv_obj_t *obj = lv_obj_create(parent_obj);
            objects.obj19 = obj;
            lv_obj_set_pos(obj, 82, 206);
            lv_obj_set_size(obj, 156, 24);
            lv_obj_set_style_bg_color(obj, lv_color_hex(theme_colors[eez_flow_get_selected_theme_index()][2]), LV_PART_MAIN | LV_STATE_DEFAULT);
            lv_obj_set_style_border_color(obj, lv_color_hex(theme_colors[eez_flow_get_selected_theme_index()][3]), LV_PART_MAIN | LV_STATE_DEFAULT);
        }
        {
            lv_obj_t *obj = lv_label_create(parent_obj);
            lv_obj_set_pos(obj, 99, 211);
            lv_obj_set_size(obj, LV_SIZE_CONTENT, LV_SIZE_CONTENT);
            lv_label_set_long_mode(obj, LV_LABEL_LONG_SCROLL);
            lv_obj_set_style_align(obj, LV_ALIGN_DEFAULT, LV_PART_MAIN | LV_STATE_DEFAULT);
            lv_obj_set_style_text_font(obj, &lv_font_montserrat_12, LV_PART_MAIN | LV_STATE_DEFAULT);
            lv_label_set_text_static(obj, "This love is so super");
        }
        {
            // wallpaperImage
            lv_obj_t *obj = lv_obj_create(parent_obj);
            objects.wallpaper_image = obj;
            lv_obj_set_pos(obj, -1, 0);
            lv_obj_set_size(obj, 320, 240);
            lv_obj_set_style_pad_left(obj, 0, LV_PART_MAIN | LV_STATE_DEFAULT);
            lv_obj_set_style_pad_top(obj, 0, LV_PART_MAIN | LV_STATE_DEFAULT);
            lv_obj_set_style_pad_right(obj, 0, LV_PART_MAIN | LV_STATE_DEFAULT);
            lv_obj_set_style_pad_bottom(obj, 0, LV_PART_MAIN | LV_STATE_DEFAULT);
            lv_obj_set_style_bg_opa(obj, 0, LV_PART_MAIN | LV_STATE_DEFAULT);
            lv_obj_set_style_border_width(obj, 0, LV_PART_MAIN | LV_STATE_DEFAULT);
            lv_obj_set_style_radius(obj, 0, LV_PART_MAIN | LV_STATE_DEFAULT);
        }
    }
    
    tick_screen_default_clock();
}

void tick_screen_default_clock() {
    void *flowState = getFlowState(0, 5);
    (void)flowState;
    {
        const char *new_val = evalTextProperty(flowState, 0, 3, "Failed to evaluate Text in Label widget");
        const char *cur_val = lv_label_get_text(objects.obj20);
        if (strcmp(new_val, cur_val) != 0) {
            tick_value_change_obj = objects.obj20;
            lv_label_set_text(objects.obj20, new_val);
            tick_value_change_obj = NULL;
        }
    }
    {
        const char *new_val = evalTextProperty(flowState, 3, 3, "Failed to evaluate Text in Label widget");
        const char *cur_val = lv_label_get_text(objects.obj21);
        if (strcmp(new_val, cur_val) != 0) {
            tick_value_change_obj = objects.obj21;
            lv_label_set_text(objects.obj21, new_val);
            tick_value_change_obj = NULL;
        }
    }
}

void create_screen_volume_pane() {
    void *flowState = getFlowState(0, 6);
    (void)flowState;
    lv_obj_t *obj = lv_obj_create(0);
    objects.volume_pane = obj;
    lv_obj_set_pos(obj, 0, 0);
    lv_obj_set_size(obj, 320, 240);
    lv_obj_set_style_bg_color(obj, lv_color_hex(theme_colors[eez_flow_get_selected_theme_index()][0]), LV_PART_MAIN | LV_STATE_DEFAULT);
    
    tick_screen_volume_pane();
}

void tick_screen_volume_pane() {
    void *flowState = getFlowState(0, 6);
    (void)flowState;
}

typedef void (*tick_screen_func_t)();
tick_screen_func_t tick_screen_funcs[] = {
    tick_screen_boot_splash,
    tick_screen_initial_qr_page,
    tick_screen_onboarding1,
    tick_screen_onboarding2,
    tick_screen_onboarding3,
    tick_screen_default_clock,
    tick_screen_volume_pane,
};
void tick_screen(int screen_index) {
    if (screen_index >= 0 && screen_index < 7) {
        tick_screen_funcs[screen_index]();
    }
}
void tick_screen_by_id(enum ScreensEnum screenId) {
    tick_screen(screenId - 1);
}

//
// Fonts
//

ext_font_desc_t fonts[] = {
    { "Nunito-18", &ui_font_nunito_18 },
    { "Nunito-18 Bold", &ui_font_nunito_18_bold },
    { "Inter-10", &ui_font_inter_10 },
    { "Inter-7", &ui_font_inter_7 },
    { "font_icons", &ui_font_font_icons },
#if LV_FONT_MONTSERRAT_8
    { "MONTSERRAT_8", &lv_font_montserrat_8 },
#endif
#if LV_FONT_MONTSERRAT_10
    { "MONTSERRAT_10", &lv_font_montserrat_10 },
#endif
#if LV_FONT_MONTSERRAT_12
    { "MONTSERRAT_12", &lv_font_montserrat_12 },
#endif
#if LV_FONT_MONTSERRAT_14
    { "MONTSERRAT_14", &lv_font_montserrat_14 },
#endif
#if LV_FONT_MONTSERRAT_16
    { "MONTSERRAT_16", &lv_font_montserrat_16 },
#endif
#if LV_FONT_MONTSERRAT_18
    { "MONTSERRAT_18", &lv_font_montserrat_18 },
#endif
#if LV_FONT_MONTSERRAT_20
    { "MONTSERRAT_20", &lv_font_montserrat_20 },
#endif
#if LV_FONT_MONTSERRAT_22
    { "MONTSERRAT_22", &lv_font_montserrat_22 },
#endif
#if LV_FONT_MONTSERRAT_24
    { "MONTSERRAT_24", &lv_font_montserrat_24 },
#endif
#if LV_FONT_MONTSERRAT_26
    { "MONTSERRAT_26", &lv_font_montserrat_26 },
#endif
#if LV_FONT_MONTSERRAT_28
    { "MONTSERRAT_28", &lv_font_montserrat_28 },
#endif
#if LV_FONT_MONTSERRAT_30
    { "MONTSERRAT_30", &lv_font_montserrat_30 },
#endif
#if LV_FONT_MONTSERRAT_32
    { "MONTSERRAT_32", &lv_font_montserrat_32 },
#endif
#if LV_FONT_MONTSERRAT_34
    { "MONTSERRAT_34", &lv_font_montserrat_34 },
#endif
#if LV_FONT_MONTSERRAT_36
    { "MONTSERRAT_36", &lv_font_montserrat_36 },
#endif
#if LV_FONT_MONTSERRAT_38
    { "MONTSERRAT_38", &lv_font_montserrat_38 },
#endif
#if LV_FONT_MONTSERRAT_40
    { "MONTSERRAT_40", &lv_font_montserrat_40 },
#endif
#if LV_FONT_MONTSERRAT_42
    { "MONTSERRAT_42", &lv_font_montserrat_42 },
#endif
#if LV_FONT_MONTSERRAT_44
    { "MONTSERRAT_44", &lv_font_montserrat_44 },
#endif
#if LV_FONT_MONTSERRAT_46
    { "MONTSERRAT_46", &lv_font_montserrat_46 },
#endif
#if LV_FONT_MONTSERRAT_48
    { "MONTSERRAT_48", &lv_font_montserrat_48 },
#endif
};

//
// Color themes
//

void change_color_theme(uint32_t theme_index) {
    {
        lv_obj_set_style_bg_color(objects.boot_splash, lv_color_hex(theme_colors[theme_index][0]), LV_PART_MAIN | LV_STATE_DEFAULT);
    }
    {
        lv_obj_set_style_bg_color(objects.initial_qr_page, lv_color_hex(theme_colors[theme_index][0]), LV_PART_MAIN | LV_STATE_DEFAULT);
        lv_obj_set_style_outline_color(objects.obj0, lv_color_hex(theme_colors[theme_index][3]), LV_PART_MAIN | LV_STATE_DEFAULT);
        lv_obj_set_style_text_color(objects.obj1, lv_color_hex(theme_colors[theme_index][5]), LV_PART_MAIN | LV_STATE_DEFAULT);
        lv_obj_set_style_text_color(objects.obj2, lv_color_hex(theme_colors[theme_index][5]), LV_PART_MAIN | LV_STATE_DEFAULT);
        lv_obj_set_style_bg_color(objects.obj5, lv_color_hex(theme_colors[theme_index][5]), LV_PART_MAIN | LV_STATE_DEFAULT);
        lv_obj_set_style_text_color(objects.obj5, lv_color_hex(theme_colors[theme_index][5]), LV_PART_MAIN | LV_STATE_DEFAULT);
        lv_obj_set_style_text_color(objects.obj6, lv_color_hex(theme_colors[theme_index][5]), LV_PART_MAIN | LV_STATE_DEFAULT);
    }
    {
        lv_obj_set_style_bg_color(objects.onboarding1, lv_color_hex(theme_colors[theme_index][0]), LV_PART_MAIN | LV_STATE_DEFAULT);
        lv_obj_set_style_text_color(objects.obj7, lv_color_hex(theme_colors[theme_index][5]), LV_PART_MAIN | LV_STATE_DEFAULT);
        lv_obj_set_style_bg_color(objects.obj8, lv_color_hex(theme_colors[theme_index][2]), LV_PART_MAIN | LV_STATE_DEFAULT);
        lv_obj_set_style_text_color(objects.obj9, lv_color_hex(theme_colors[theme_index][5]), LV_PART_MAIN | LV_STATE_DEFAULT);
        lv_obj_set_style_text_color(objects.obj10, lv_color_hex(theme_colors[theme_index][5]), LV_PART_MAIN | LV_STATE_DEFAULT);
    }
    {
        lv_obj_set_style_bg_color(objects.onboarding2, lv_color_hex(theme_colors[theme_index][0]), LV_PART_MAIN | LV_STATE_DEFAULT);
        lv_obj_set_style_text_color(objects.obj11, lv_color_hex(theme_colors[theme_index][5]), LV_PART_MAIN | LV_STATE_DEFAULT);
        lv_obj_set_style_bg_color(objects.obj12, lv_color_hex(theme_colors[theme_index][2]), LV_PART_MAIN | LV_STATE_DEFAULT);
        lv_obj_set_style_text_color(objects.obj13, lv_color_hex(theme_colors[theme_index][5]), LV_PART_MAIN | LV_STATE_DEFAULT);
        lv_obj_set_style_text_color(objects.obj14, lv_color_hex(theme_colors[theme_index][5]), LV_PART_MAIN | LV_STATE_DEFAULT);
    }
    {
        lv_obj_set_style_bg_color(objects.onboarding3, lv_color_hex(theme_colors[theme_index][0]), LV_PART_MAIN | LV_STATE_DEFAULT);
        lv_obj_set_style_text_color(objects.obj15, lv_color_hex(theme_colors[theme_index][5]), LV_PART_MAIN | LV_STATE_DEFAULT);
        lv_obj_set_style_bg_color(objects.obj16, lv_color_hex(theme_colors[theme_index][1]), LV_PART_MAIN | LV_STATE_DEFAULT);
        lv_obj_set_style_text_color(objects.obj17, lv_color_hex(theme_colors[theme_index][5]), LV_PART_MAIN | LV_STATE_DEFAULT);
        lv_obj_set_style_text_color(objects.obj18, lv_color_hex(theme_colors[theme_index][5]), LV_PART_MAIN | LV_STATE_DEFAULT);
    }
    {
        lv_obj_set_style_bg_color(objects.default_clock, lv_color_hex(theme_colors[theme_index][0]), LV_PART_MAIN | LV_STATE_DEFAULT);
        lv_obj_set_style_bg_color(objects.obj19, lv_color_hex(theme_colors[theme_index][2]), LV_PART_MAIN | LV_STATE_DEFAULT);
        lv_obj_set_style_border_color(objects.obj19, lv_color_hex(theme_colors[theme_index][3]), LV_PART_MAIN | LV_STATE_DEFAULT);
    }
    {
        lv_obj_set_style_bg_color(objects.volume_pane, lv_color_hex(theme_colors[theme_index][0]), LV_PART_MAIN | LV_STATE_DEFAULT);
    }
    lv_obj_invalidate(objects.boot_splash);
    lv_obj_invalidate(objects.initial_qr_page);
    lv_obj_invalidate(objects.onboarding1);
    lv_obj_invalidate(objects.onboarding2);
    lv_obj_invalidate(objects.onboarding3);
    lv_obj_invalidate(objects.default_clock);
    lv_obj_invalidate(objects.volume_pane);
}
static const char *theme_names[] = { "Dark Mode", "Light Mode" };
uint32_t theme_colors[2][13] = {
    { 0xff0d0d0d, 0xff1a1a1a, 0xff222222, 0xff2a2a2a, 0xff333333, 0xfff0f0f0, 0xff888888, 0xff444444, 0xff1db954, 0xff4ade80, 0xffffb347, 0xffe63946, 0xffffffff },
    { 0xfffaf1f9, 0xffffffff, 0xffffdef2, 0xfffdb6e1, 0xffe8c8e0, 0xff010a1a, 0xff6b3a6b, 0xffc4a8c4, 0xff1db954, 0xff16a34a, 0xffd97706, 0xffdc2626, 0xffffffff },
};

//
//
//

void create_screens() {
    
    eez_flow_init_fonts(fonts, sizeof(fonts) / sizeof(ext_font_desc_t));
    
    eez_flow_init_themes(theme_names, sizeof(theme_names) / sizeof(const char *), change_color_theme, &theme_colors[0][0], sizeof(theme_colors[0]) / sizeof(uint32_t));

// Set default LVGL theme
    lv_disp_t *dispp = lv_disp_get_default();
    lv_theme_t *theme = lv_theme_default_init(dispp, lv_palette_main(LV_PALETTE_BLUE), lv_palette_main(LV_PALETTE_RED), false, LV_FONT_DEFAULT);
    lv_disp_set_theme(dispp, theme);
    
    // Initialize screens
    eez_flow_init_screen_names(screen_names, sizeof(screen_names) / sizeof(const char *));
    eez_flow_init_object_names(object_names, sizeof(object_names) / sizeof(const char *));
    
    // Create screens
    create_screen_boot_splash();
    create_screen_initial_qr_page();
    create_screen_onboarding1();
    create_screen_onboarding2();
    create_screen_onboarding3();
    create_screen_default_clock();
    create_screen_volume_pane();
}
