serenebliss0/wavelet/src/mini/wavelet-mini-screens/src/ui/ui_font_inter_7.c

/*******************************************************************************
 * Size: 7 px
 * Bpp: 8
 * Opts: --bpp 8 --size 7 --no-compress --font ..\..\..\..\..\..\Inter,Nunito\Inter\Inter-VariableFont_opsz,wght.ttf --range 32-127 --format lvgl
 ******************************************************************************/

#ifdef __has_include
    #if __has_include("lvgl.h")
        #ifndef LV_LVGL_H_INCLUDE_SIMPLE
            #define LV_LVGL_H_INCLUDE_SIMPLE
        #endif
    #endif
#endif

#ifdef LV_LVGL_H_INCLUDE_SIMPLE
    #include "lvgl.h"
#else
    #include "lvgl.h"
#endif

#ifndef UI_FONT_INTER_7
#define UI_FONT_INTER_7 1
#endif

#if UI_FONT_INTER_7

/*-----------------
 *    BITMAPS
 *----------------*/

/*Store the image of the glyphs*/
static LV_ATTRIBUTE_LARGE_CONST const uint8_t glyph_bitmap[] = {
    /* U+0020 " " */

    /* U+0021 "!" */
    0x57, 0x59, 0x53, 0x56, 0x50, 0x53, 0x2b, 0x2d,
    0x4e, 0x50,

    /* U+0022 "\"" */
    0x44, 0x77, 0x86, 0x39, 0x65, 0x7c,

    /* U+0023 "#" */
    0x0, 0x84, 0x0, 0x84, 0x0, 0x4b, 0xff, 0x8f,
    0xff, 0x26, 0x0, 0x83, 0x26, 0x5d, 0x0, 0x8e,
    0xf0, 0xd9, 0xb7, 0x0, 0x46, 0x3d, 0x79, 0xa,
    0x0,

    /* U+0024 "$" */
    0x0, 0x0, 0x49, 0x0, 0x0, 0x1f, 0xa4, 0xff,
    0x7c, 0x0, 0x62, 0x4c, 0x68, 0x32, 0x0, 0x7,
    0x71, 0xf4, 0x53, 0x0, 0x35, 0xe, 0x68, 0xa1,
    0x7, 0x2f, 0xa7, 0xff, 0x8a, 0x0, 0x0, 0x0,
    0x45, 0x0, 0x0,

    /* U+0025 "%" */
    0x1e, 0x97, 0x80, 0x0, 0x6f, 0x25, 0x0, 0xf,
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
    0x52, 0x6f, 0x0, 0x0, 0x96, 0x0, 0x0, 0x9d,
    0x0, 0x0, 0x92, 0xac, 0x0, 0x9c, 0x0, 0x0,
    0x9a, 0x0, 0x52, 0x4e, 0x0,

    /* U+007E "~" */
    0x1c, 0x9c, 0x3a, 0x5a, 0x2, 0x3d, 0x1c, 0x72,
    0x82, 0x0
};

/*---------------------
 *  GLYPH DESCRIPTION
 *--------------------*/

static const lv_font_fmt_txt_glyph_dsc_t glyph_dsc[] = {
    {.bitmap_index = 0, .adv_w = 0, .box_w = 0, .box_h = 0, .ofs_x = 0, .ofs_y = 0} /* id = 0 reserved */,
    {.bitmap_index = 0, .adv_w = 32, .box_w = 0, .box_h = 0, .ofs_x = 0, .ofs_y = 0},
    {.bitmap_index = 0, .adv_w = 32, .box_w = 2, .box_h = 5, .ofs_x = 0, .ofs_y = 0},
    {.bitmap_index = 10, .adv_w = 52, .box_w = 3, .box_h = 2, .ofs_x = 0, .ofs_y = 3},
    {.bitmap_index = 16, .adv_w = 71, .box_w = 5, .box_h = 5, .ofs_x = 0, .ofs_y = 0},
    {.bitmap_index = 41, .adv_w = 72, .box_w = 5, .box_h = 7, .ofs_x = 0, .ofs_y = -1},
    {.bitmap_index = 76, .adv_w = 110, .box_w = 7, .box_h = 5, .ofs_x = 0, .ofs_y = 0},
    {.bitmap_index = 111, .adv_w = 72, .box_w = 5, .box_h = 5, .ofs_x = 0, .ofs_y = 0},
    {.bitmap_index = 136, .adv_w = 34, .box_w = 2, .box_h = 2, .ofs_x = 0, .ofs_y = 3},
    {.bitmap_index = 140, .adv_w = 41, .box_w = 3, .box_h = 7, .ofs_x = 0, .ofs_y = -1},
    {.bitmap_index = 161, .adv_w = 41, .box_w = 2, .box_h = 7, .ofs_x = 0, .ofs_y = -1},
    {.bitmap_index = 175, .adv_w = 56, .box_w = 4, .box_h = 3, .ofs_x = 0, .ofs_y = 2},
    {.bitmap_index = 187, .adv_w = 74, .box_w = 4, .box_h = 5, .ofs_x = 0, .ofs_y = 0},
    {.bitmap_index = 207, .adv_w = 32, .box_w = 2, .box_h = 2, .ofs_x = 0, .ofs_y = -1},
    {.bitmap_index = 211, .adv_w = 52, .box_w = 3, .box_h = 1, .ofs_x = 0, .ofs_y = 2},
    {.bitmap_index = 214, .adv_w = 32, .box_w = 2, .box_h = 1, .ofs_x = 0, .ofs_y = 0},
    {.bitmap_index = 216, .adv_w = 40, .box_w = 3, .box_h = 7, .ofs_x = 0, .ofs_y = -1},
    {.bitmap_index = 237, .adv_w = 71, .box_w = 4, .box_h = 5, .ofs_x = 0, .ofs_y = 0},
    {.bitmap_index = 257, .adv_w = 46, .box_w = 3, .box_h = 5, .ofs_x = 0, .ofs_y = 0},
    {.bitmap_index = 272, .adv_w = 68, .box_w = 4, .box_h = 5, .ofs_x = 0, .ofs_y = 0},
    {.bitmap_index = 292, .adv_w = 69, .box_w = 4, .box_h = 5, .ofs_x = 0, .ofs_y = 0},
    {.bitmap_index = 312, .adv_w = 72, .box_w = 5, .box_h = 5, .ofs_x = 0, .ofs_y = 0},
    {.bitmap_index = 337, .adv_w = 66, .box_w = 4, .box_h = 5, .ofs_x = 0, .ofs_y = 0},
    {.bitmap_index = 357, .adv_w = 69, .box_w = 4, .box_h = 5, .ofs_x = 0, .ofs_y = 0},
    {.bitmap_index = 377, .adv_w = 63, .box_w = 4, .box_h = 5, .ofs_x = 0, .ofs_y = 0},
    {.bitmap_index = 397, .adv_w = 69, .box_w = 4, .box_h = 5, .ofs_x = 0, .ofs_y = 0},
    {.bitmap_index = 417, .adv_w = 69, .box_w = 4, .box_h = 5, .ofs_x = 0, .ofs_y = 0},
    {.bitmap_index = 437, .adv_w = 32, .box_w = 2, .box_h = 4, .ofs_x = 0, .ofs_y = 0},
    {.bitmap_index = 445, .adv_w = 34, .box_w = 2, .box_h = 5, .ofs_x = 0, .ofs_y = -1},
    {.bitmap_index = 455, .adv_w = 74, .box_w = 4, .box_h = 4, .ofs_x = 0, .ofs_y = 0},
    {.bitmap_index = 471, .adv_w = 74, .box_w = 4, .box_h = 3, .ofs_x = 0, .ofs_y = 1},
    {.bitmap_index = 483, .adv_w = 74, .box_w = 5, .box_h = 4, .ofs_x = 0, .ofs_y = 0},
    {.bitmap_index = 503, .adv_w = 57, .box_w = 4, .box_h = 5, .ofs_x = 0, .ofs_y = 0},
    {.bitmap_index = 523, .adv_w = 108, .box_w = 7, .box_h = 7, .ofs_x = 0, .ofs_y = -1},
    {.bitmap_index = 572, .adv_w = 77, .box_w = 5, .box_h = 5, .ofs_x = 0, .ofs_y = 0},
    {.bitmap_index = 597, .adv_w = 73, .box_w = 5, .box_h = 5, .ofs_x = 0, .ofs_y = 0},
    {.bitmap_index = 622, .adv_w = 82, .box_w = 5, .box_h = 5, .ofs_x = 0, .ofs_y = 0},
    {.bitmap_index = 647, .adv_w = 81, .box_w = 5, .box_h = 5, .ofs_x = 0, .ofs_y = 0},
    {.bitmap_index = 672, .adv_w = 67, .box_w = 4, .box_h = 5, .ofs_x = 0, .ofs_y = 0},
    {.bitmap_index = 692, .adv_w = 66, .box_w = 4, .box_h = 5, .ofs_x = 0, .ofs_y = 0},
    {.bitmap_index = 712, .adv_w = 84, .box_w = 5, .box_h = 5, .ofs_x = 0, .ofs_y = 0},
    {.bitmap_index = 737, .adv_w = 83, .box_w = 5, .box_h = 5, .ofs_x = 0, .ofs_y = 0},
    {.bitmap_index = 762, .adv_w = 30, .box_w = 2, .box_h = 5, .ofs_x = 0, .ofs_y = 0},
    {.bitmap_index = 772, .adv_w = 64, .box_w = 4, .box_h = 5, .ofs_x = 0, .ofs_y = 0},
    {.bitmap_index = 792, .adv_w = 75, .box_w = 5, .box_h = 5, .ofs_x = 0, .ofs_y = 0},
    {.bitmap_index = 817, .adv_w = 63, .box_w = 4, .box_h = 5, .ofs_x = 0, .ofs_y = 0},
    {.bitmap_index = 837, .adv_w = 101, .box_w = 6, .box_h = 5, .ofs_x = 0, .ofs_y = 0},
    {.bitmap_index = 867, .adv_w = 84, .box_w = 5, .box_h = 5, .ofs_x = 0, .ofs_y = 0},
    {.bitmap_index = 892, .adv_w = 86, .box_w = 5, .box_h = 5, .ofs_x = 0, .ofs_y = 0},
    {.bitmap_index = 917, .adv_w = 72, .box_w = 5, .box_h = 5, .ofs_x = 0, .ofs_y = 0},
    {.bitmap_index = 942, .adv_w = 86, .box_w = 5, .box_h = 6, .ofs_x = 0, .ofs_y = -1},
    {.bitmap_index = 972, .adv_w = 72, .box_w = 5, .box_h = 5, .ofs_x = 0, .ofs_y = 0},
    {.bitmap_index = 997, .adv_w = 72, .box_w = 5, .box_h = 5, .ofs_x = 0, .ofs_y = 0},
    {.bitmap_index = 1022, .adv_w = 72, .box_w = 5, .box_h = 5, .ofs_x = 0, .ofs_y = 0},
    {.bitmap_index = 1047, .adv_w = 83, .box_w = 5, .box_h = 5, .ofs_x = 0, .ofs_y = 0},
    {.bitmap_index = 1072, .adv_w = 77, .box_w = 5, .box_h = 5, .ofs_x = 0, .ofs_y = 0},
    {.bitmap_index = 1097, .adv_w = 110, .box_w = 7, .box_h = 5, .ofs_x = 0, .ofs_y = 0},
    {.bitmap_index = 1132, .adv_w = 76, .box_w = 5, .box_h = 5, .ofs_x = 0, .ofs_y = 0},
    {.bitmap_index = 1157, .adv_w = 76, .box_w = 5, .box_h = 5, .ofs_x = 0, .ofs_y = 0},
    {.bitmap_index = 1182, .adv_w = 70, .box_w = 4, .box_h = 5, .ofs_x = 0, .ofs_y = 0},
    {.bitmap_index = 1202, .adv_w = 41, .box_w = 3, .box_h = 7, .ofs_x = 0, .ofs_y = -1},
    {.bitmap_index = 1223, .adv_w = 40, .box_w = 3, .box_h = 7, .ofs_x = 0, .ofs_y = -1},
    {.bitmap_index = 1244, .adv_w = 41, .box_w = 2, .box_h = 7, .ofs_x = 0, .ofs_y = -1},
    {.bitmap_index = 1258, .adv_w = 53, .box_w = 4, .box_h = 3, .ofs_x = 0, .ofs_y = 2},
    {.bitmap_index = 1270, .adv_w = 51, .box_w = 4, .box_h = 1, .ofs_x = 0, .ofs_y = -1},
    {.bitmap_index = 1274, .adv_w = 36, .box_w = 2, .box_h = 2, .ofs_x = 0, .ofs_y = 4},
    {.bitmap_index = 1278, .adv_w = 63, .box_w = 4, .box_h = 4, .ofs_x = 0, .ofs_y = 0},
    {.bitmap_index = 1294, .adv_w = 69, .box_w = 4, .box_h = 5, .ofs_x = 0, .ofs_y = 0},
    {.bitmap_index = 1314, .adv_w = 64, .box_w = 4, .box_h = 4, .ofs_x = 0, .ofs_y = 0},
    {.bitmap_index = 1330, .adv_w = 69, .box_w = 4, .box_h = 5, .ofs_x = 0, .ofs_y = 0},
    {.bitmap_index = 1350, .adv_w = 65, .box_w = 4, .box_h = 4, .ofs_x = 0, .ofs_y = 0},
    {.bitmap_index = 1366, .adv_w = 41, .box_w = 3, .box_h = 5, .ofs_x = 0, .ofs_y = 0},
    {.bitmap_index = 1381, .adv_w = 69, .box_w = 4, .box_h = 5, .ofs_x = 0, .ofs_y = -1},
    {.bitmap_index = 1401, .adv_w = 66, .box_w = 4, .box_h = 5, .ofs_x = 0, .ofs_y = 0},
    {.bitmap_index = 1421, .adv_w = 27, .box_w = 2, .box_h = 5, .ofs_x = 0, .ofs_y = 0},
    {.bitmap_index = 1431, .adv_w = 27, .box_w = 3, .box_h = 6, .ofs_x = -1, .ofs_y = -1},
    {.bitmap_index = 1449, .adv_w = 61, .box_w = 4, .box_h = 5, .ofs_x = 0, .ofs_y = 0},
    {.bitmap_index = 1469, .adv_w = 27, .box_w = 2, .box_h = 5, .ofs_x = 0, .ofs_y = 0},
    {.bitmap_index = 1479, .adv_w = 98, .box_w = 6, .box_h = 4, .ofs_x = 0, .ofs_y = 0},
    {.bitmap_index = 1503, .adv_w = 66, .box_w = 4, .box_h = 4, .ofs_x = 0, .ofs_y = 0},
    {.bitmap_index = 1519, .adv_w = 67, .box_w = 4, .box_h = 4, .ofs_x = 0, .ofs_y = 0},
    {.bitmap_index = 1535, .adv_w = 69, .box_w = 4, .box_h = 5, .ofs_x = 0, .ofs_y = -1},
    {.bitmap_index = 1555, .adv_w = 69, .box_w = 4, .box_h = 5, .ofs_x = 0, .ofs_y = -1},
    {.bitmap_index = 1575, .adv_w = 42, .box_w = 3, .box_h = 4, .ofs_x = 0, .ofs_y = 0},
    {.bitmap_index = 1587, .adv_w = 59, .box_w = 4, .box_h = 4, .ofs_x = 0, .ofs_y = 0},
    {.bitmap_index = 1603, .adv_w = 37, .box_w = 3, .box_h = 5, .ofs_x = 0, .ofs_y = 0},
    {.bitmap_index = 1618, .adv_w = 66, .box_w = 4, .box_h = 4, .ofs_x = 0, .ofs_y = 0},
    {.bitmap_index = 1634, .adv_w = 63, .box_w = 4, .box_h = 4, .ofs_x = 0, .ofs_y = 0},
    {.bitmap_index = 1650, .adv_w = 92, .box_w = 6, .box_h = 4, .ofs_x = 0, .ofs_y = 0},
    {.bitmap_index = 1674, .adv_w = 61, .box_w = 4, .box_h = 4, .ofs_x = 0, .ofs_y = 0},
    {.bitmap_index = 1690, .adv_w = 63, .box_w = 4, .box_h = 5, .ofs_x = 0, .ofs_y = -1},
    {.bitmap_index = 1710, .adv_w = 62, .box_w = 4, .box_h = 4, .ofs_x = 0, .ofs_y = 0},
    {.bitmap_index = 1726, .adv_w = 48, .box_w = 3, .box_h = 7, .ofs_x = 0, .ofs_y = -2},
    {.bitmap_index = 1747, .adv_w = 37, .box_w = 2, .box_h = 9, .ofs_x = 0, .ofs_y = -2},
    {.bitmap_index = 1765, .adv_w = 48, .box_w = 3, .box_h = 7, .ofs_x = 0, .ofs_y = -2},
    {.bitmap_index = 1786, .adv_w = 74, .box_w = 5, .box_h = 2, .ofs_x = 0, .ofs_y = 1}
};

/*---------------------
 *  CHARACTER MAPPING
 *--------------------*/

/*Collect the unicode lists and glyph_id offsets*/
static const lv_font_fmt_txt_cmap_t cmaps[] =
{
    {
        .range_start = 32, .range_length = 95, .glyph_id_start = 1,
        .unicode_list = NULL, .glyph_id_ofs_list = NULL, .list_length = 0, .type = LV_FONT_FMT_TXT_CMAP_FORMAT0_TINY
    }
};

/*-----------------
 *    KERNING
 *----------------*/

/*Pair left and right glyphs for kerning*/
static const uint8_t kern_pair_glyph_ids[] =
{
    3, 7,
    3, 13,
    3, 15,
    3, 21,
    7, 3,
    7, 8,
    7, 61,
    8, 7,
    8, 13,
    8, 15,
    8, 21,
    11, 7,
    11, 13,
    11, 15,
    11, 21,
    11, 33,
    11, 64,
    12, 19,
    12, 20,
    12, 24,
    12, 61,
    13, 3,
    13, 8,
    13, 17,
    13, 18,
    13, 20,
    13, 22,
    13, 23,
    13, 24,
    13, 25,
    13, 26,
    13, 32,
    13, 33,
    14, 19,
    14, 20,
    14, 24,
    14, 61,
    15, 3,
    15, 8,
    15, 17,
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
};

/* Kerning between the respective left and right glyphs
 * 4.4 format which needs to scaled with `kern_scale`*/
static const int8_t kern_pair_values[] =
{
    -4, -9, -9, -7, -4, -4, -7, -4,
    -9, -9, -7, -4, -15, -15, -5, -1,
    -8, -4, -1, -3, -6, -9, -9, -3,
    -10, -3, -2, -3, -2, -3, -1, -10,
    -5, -4, -1, -3, -6, -9, -9, -3,
    -10, -3, -2, -3, -2, -3, -1, -10,
    -5, -4, -4, -3, -3, -2, -1, -5,
    -2, -2, -3, -3, -2, -2, -4, -4,
    -2, -2, -3, -3, -4, -4, -5, -6,
    -5, -14, -14, -2, -2, -7, -1, -2,
    2, -2, -1, -4, -4, -10, -18, -2,
    -3, -3, -2, -3, -3, -2, -1, -5,
    -7, -7, -8, -8, -8, -5, -5, -4,
    -4, -4, -9, -9, -9, -4, -4, 2,
    -4, -6, -7, -4, -5, -9, -4, -4,
    -15, -15, -5, -1, -8, -8, -5, -12,
    -5, -6, -5, -5, -5, -5, -4, -9,
    -8, 4, -4, -1, -3, -6
};

/*Collect the kern pair's data in one place*/
static const lv_font_fmt_txt_kern_pair_t kern_pairs =
{
    .glyph_ids = kern_pair_glyph_ids,
    .values = kern_pair_values,
    .pair_cnt = 142,
    .glyph_ids_size = 0
};

/*--------------------
 *  ALL CUSTOM DATA
 *--------------------*/

#if LVGL_VERSION_MAJOR == 8
/*Store all the custom data of the font*/
static  lv_font_fmt_txt_glyph_cache_t cache;
#endif

#if LVGL_VERSION_MAJOR >= 8
static const lv_font_fmt_txt_dsc_t font_dsc = {
#else
static lv_font_fmt_txt_dsc_t font_dsc = {
#endif
    .glyph_bitmap = glyph_bitmap,
    .glyph_dsc = glyph_dsc,
    .cmaps = cmaps,
    .kern_dsc = &kern_pairs,
    .kern_scale = 16,
    .cmap_num = 1,
    .bpp = 8,
    .kern_classes = 0,
    .bitmap_format = 0,
#if LVGL_VERSION_MAJOR == 8
    .cache = &cache
#endif
};

/*-----------------
 *  PUBLIC FONT
 *----------------*/

/*Initialize a public general font descriptor*/
#if LVGL_VERSION_MAJOR >= 8
const lv_font_t ui_font_inter_7 = {
#else
lv_font_t ui_font_inter_7 = {
#endif
    .get_glyph_dsc = lv_font_get_glyph_dsc_fmt_txt,    /*Function pointer to get glyph's data*/
    .get_glyph_bitmap = lv_font_get_bitmap_fmt_txt,    /*Function pointer to get glyph's bitmap*/
    .line_height = 9,          /*The maximum line height required by the font*/
    .base_line = 2,             /*Baseline measured from the bottom of the line*/
#if !(LVGL_VERSION_MAJOR == 6 && LVGL_VERSION_MINOR == 0)
    .subpx = LV_FONT_SUBPX_NONE,
#endif
#if LV_VERSION_CHECK(7, 4, 0) || LVGL_VERSION_MAJOR >= 8
    .underline_position = -1,
    .underline_thickness = 0,
#endif
    .dsc = &font_dsc,          /*The custom font data. Will be accessed by `get_glyph_bitmap/dsc` */
#if LV_VERSION_CHECK(8, 2, 0) || LVGL_VERSION_MAJOR >= 9
    .fallback = NULL,
#endif
    .user_data = NULL,
};

#endif /*#if UI_FONT_INTER_7*/
