serenebliss0/wavelet/src/mini/wavelet-mini-screens/src/ui/ui_image_mini_manual_code_box_initialpair.c

#ifdef __has_include
    #if __has_include("lvgl.h")
        #ifndef LV_LVGL_H_INCLUDE_SIMPLE
            #define LV_LVGL_H_INCLUDE_SIMPLE
        #endif
    #endif
#endif
#ifdef __has_include
    #if __has_include("lvgl.h")
        #ifndef LV_LVGL_H_INCLUDE_SIMPLE
            #define LV_LVGL_H_INCLUDE_SIMPLE
        #endif
    #endif
#endif

#if defined(LV_LVGL_H_INCLUDE_SIMPLE)
    #include "lvgl.h"
#else
    #include "lvgl/lvgl.h"
#endif

#ifndef LV_ATTRIBUTE_MEM_ALIGN
#define LV_ATTRIBUTE_MEM_ALIGN
#endif

#ifndef LV_ATTRIBUTE_IMG_IMG_MINI_MANUAL_CODE_BOX_INITIALPAIR
#define LV_ATTRIBUTE_IMG_IMG_MINI_MANUAL_CODE_BOX_INITIALPAIR
#endif

const LV_ATTRIBUTE_MEM_ALIGN LV_ATTRIBUTE_LARGE_CONST LV_ATTRIBUTE_IMG_IMG_MINI_MANUAL_CODE_BOX_INITIALPAIR uint8_t img_mini_manual_code_box_initialpair_map[] = {
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
  
};

const lv_img_dsc_t img_mini_manual_code_box_initialpair = {
  .header.cf = LV_IMG_CF_RGB565A8,
  .header.always_zero = 0,
  .header.reserved = 0,
  .header.w = 163,
  .header.h = 62,
  .data_size = 30318,
  .data = img_mini_manual_code_box_initialpair_map,
};
