serenebliss0/wavelet/src/mini/wavelet-mini-screens/src/ui/ui_image_onboarding_tutorial_1_swipedown.c

#ifdef __has_include
    #if __has_include("lvgl.h")
        #ifndef LV_LVGL_H_INCLUDE_SIMPLE
            #define LV_LVGL_H_INCLUDE_SIMPLE
        #endif
    #endif
#endif
#ifdef __has_include
    #if __has_include("lvgl.h")
        #ifndef LV_LVGL_H_INCLUDE_SIMPLE
            #define LV_LVGL_H_INCLUDE_SIMPLE
        #endif
    #endif
#endif

#if defined(LV_LVGL_H_INCLUDE_SIMPLE)
    #include "lvgl.h"
#else
    #include "lvgl/lvgl.h"
#endif

#ifndef LV_ATTRIBUTE_MEM_ALIGN
#define LV_ATTRIBUTE_MEM_ALIGN
#endif

#ifndef LV_ATTRIBUTE_IMG_IMG_ONBOARDING_TUTORIAL_1_SWIPEDOWN
#define LV_ATTRIBUTE_IMG_IMG_ONBOARDING_TUTORIAL_1_SWIPEDOWN
#endif

const LV_ATTRIBUTE_MEM_ALIGN LV_ATTRIBUTE_LARGE_CONST LV_ATTRIBUTE_IMG_IMG_ONBOARDING_TUTORIAL_1_SWIPEDOWN uint8_t img_onboarding_tutorial_1_swipedown_map[] = {
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
